TylerRamsawak/Motorola-MicroTAC-4G-LTE-Retrofit/3D_back_np.png

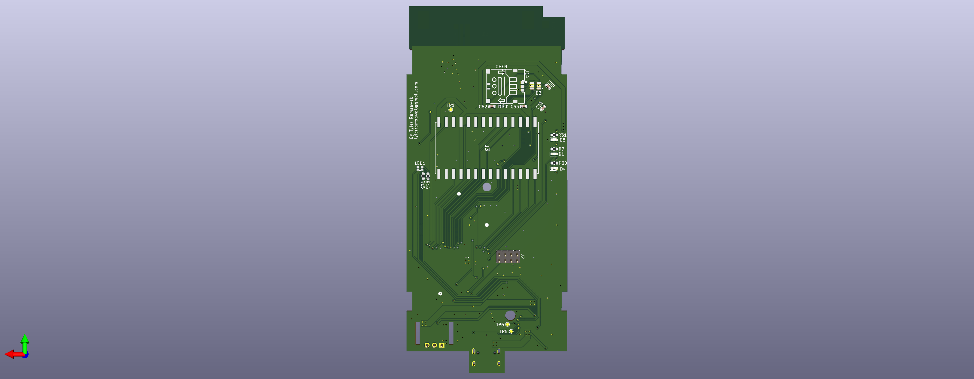
3D_back_np.png
